rfmaynard/Accel-MagnetoMeter/images/IMG_20181023_001222.jpg

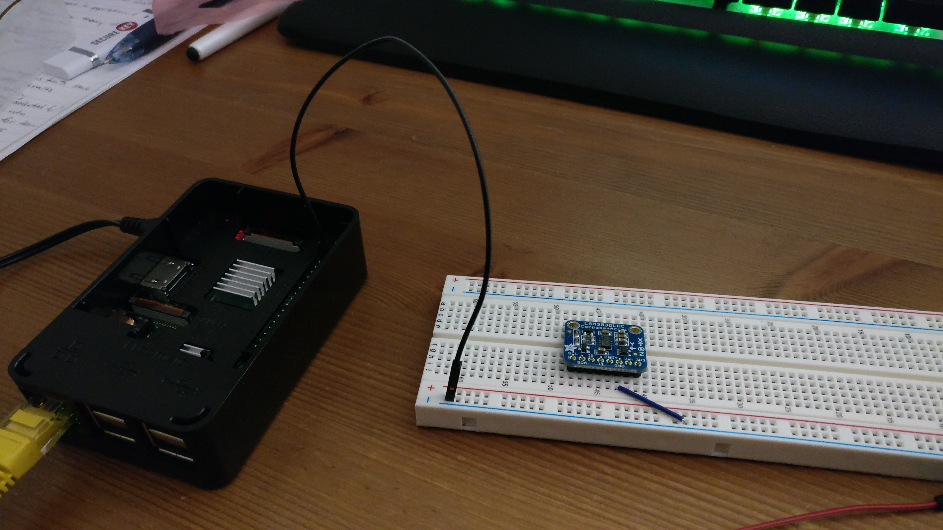
images/IMG_20181023_001222.jpg
