rfmaynard/Accel-MagnetoMeter/images/IMG_20181023_002304.jpg

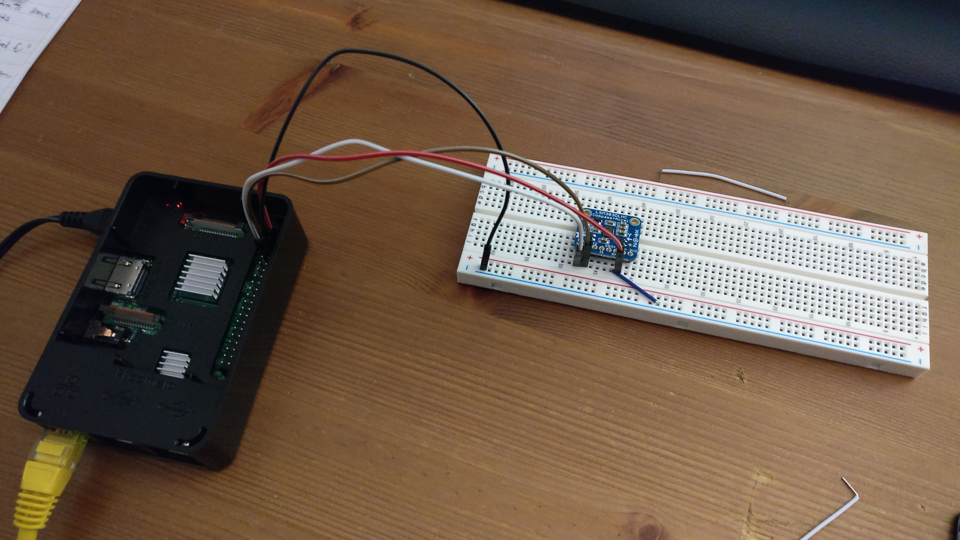
images/IMG_20181023_002304.jpg
