rfmaynard/Accel-MagnetoMeter/images/IMG_20181023_112441.jpg

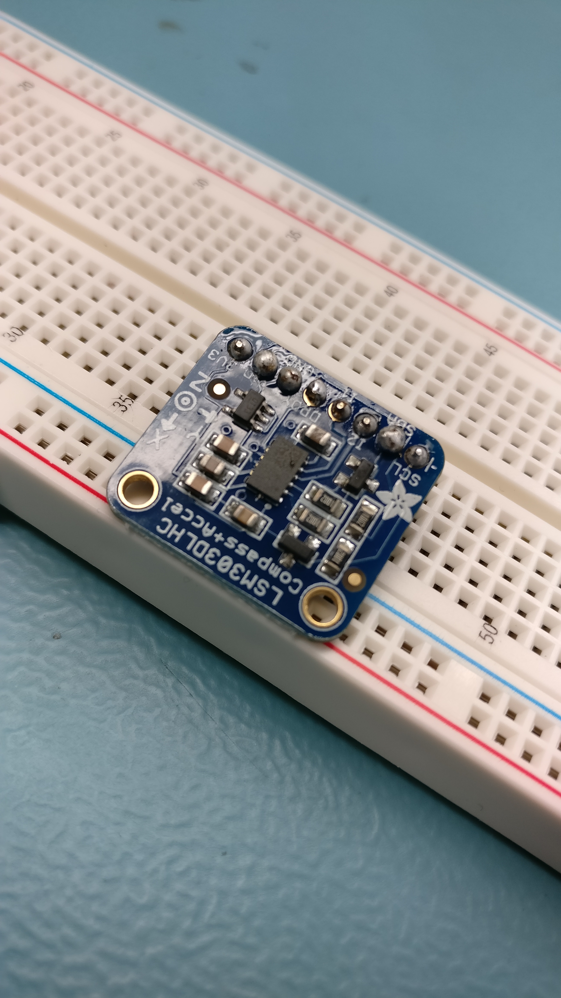
images/IMG_20181023_112441.jpg
