rfmaynard/Accel-MagnetoMeter/images/IMG_20181023_121612.jpg

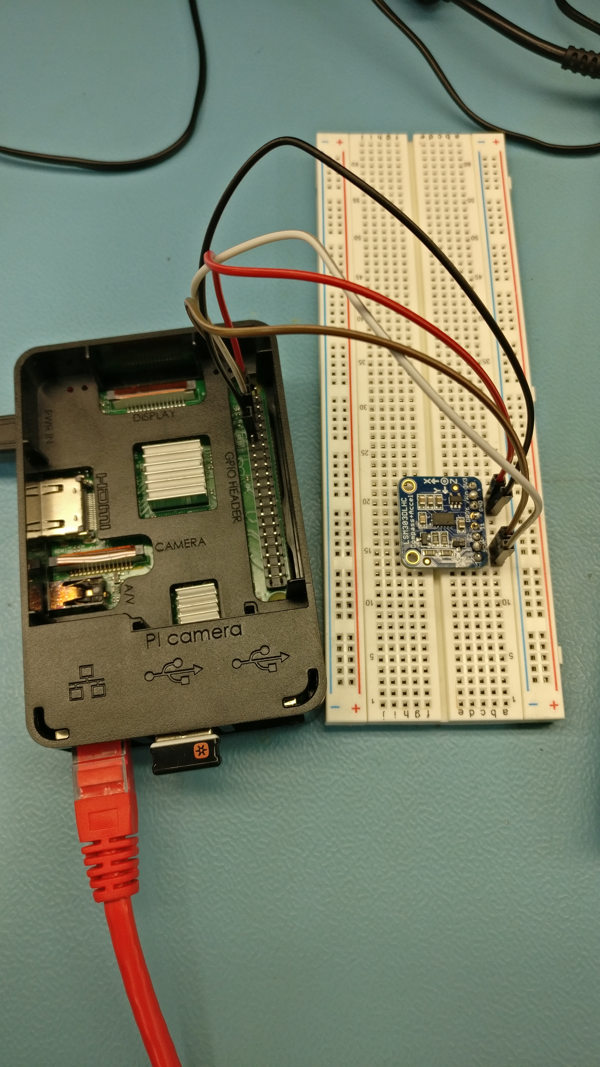
images/IMG_20181023_121612.jpg
