rfmaynard/Accel-MagnetoMeter/images/IMG_20181106_105713.jpg

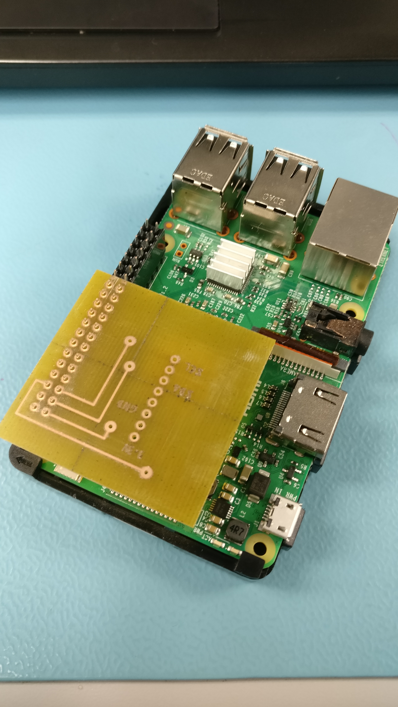
images/IMG_20181106_105713.jpg
