rfmaynard/Accel-MagnetoMeter/images/IMG_20181106_105935.jpg

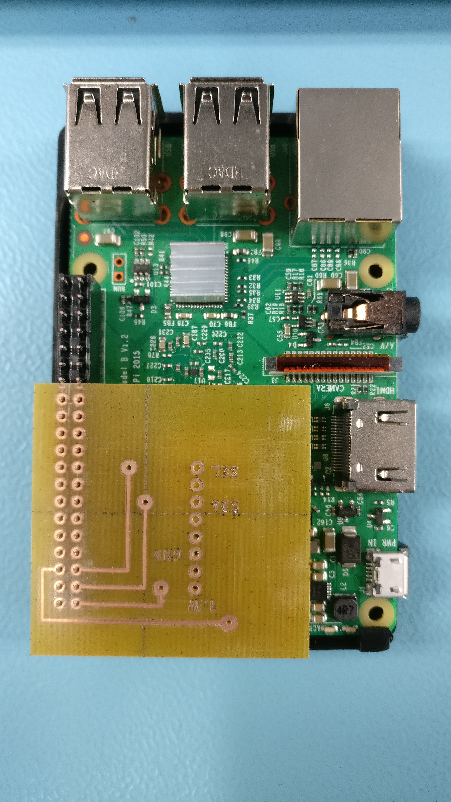
images/IMG_20181106_105935.jpg
