rfmaynard/Accel-MagnetoMeter/images/IMG_20181106_105943.jpg

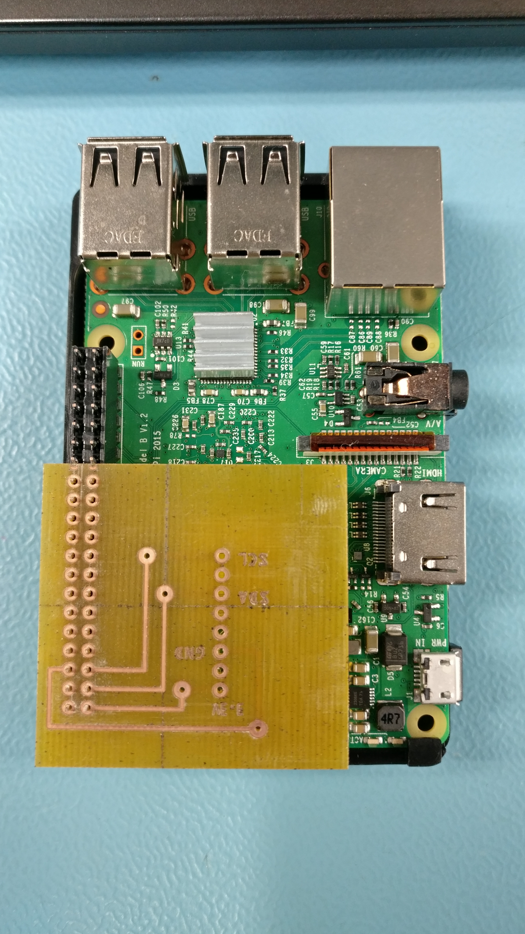
images/IMG_20181106_105943.jpg
