rfmaynard/Accel-MagnetoMeter/images/IMG_20181106_113040.jpg

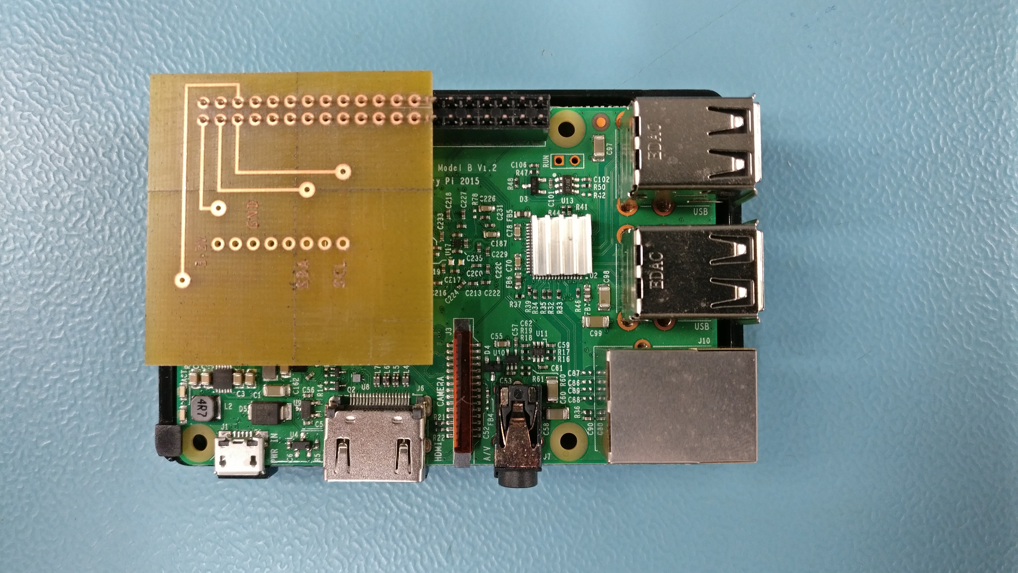
images/IMG_20181106_113040.jpg
