rfmaynard/Accel-MagnetoMeter/images/IMG_20181106_114735.jpg

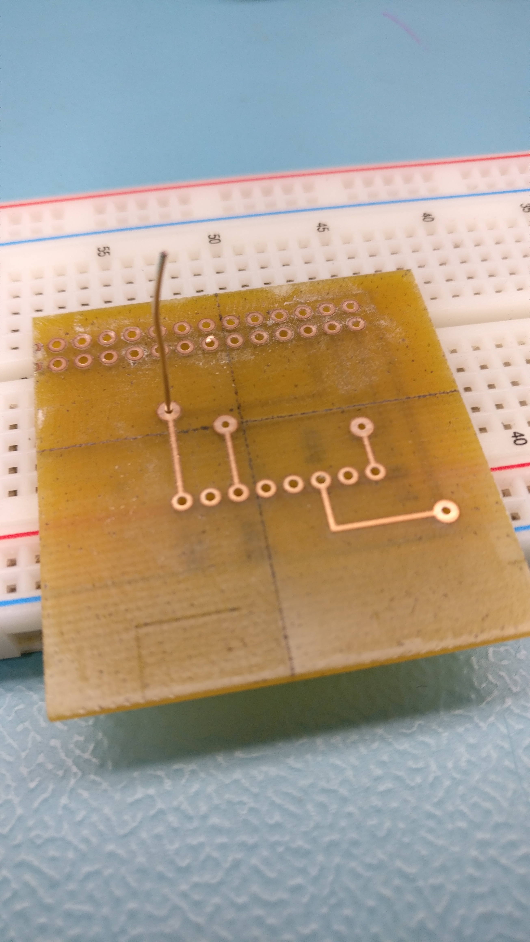
images/IMG_20181106_114735.jpg
