rfmaynard/Accel-MagnetoMeter/images/IMG_20181106_120816.jpg

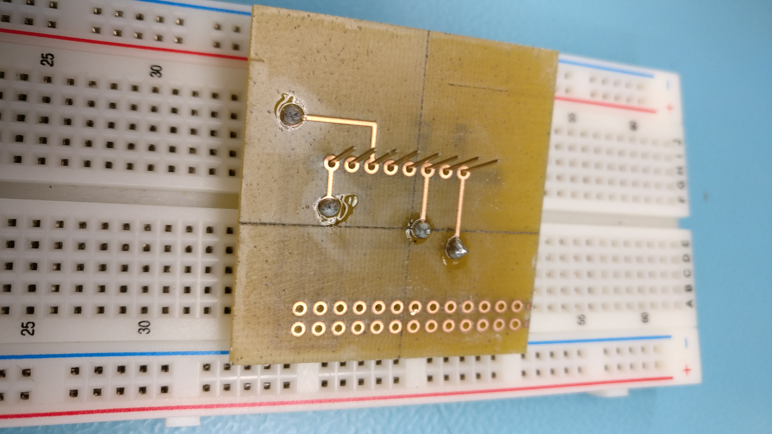
images/IMG_20181106_120816.jpg
