rfmaynard/Accel-MagnetoMeter/images/IMG_20181113_110009.jpg

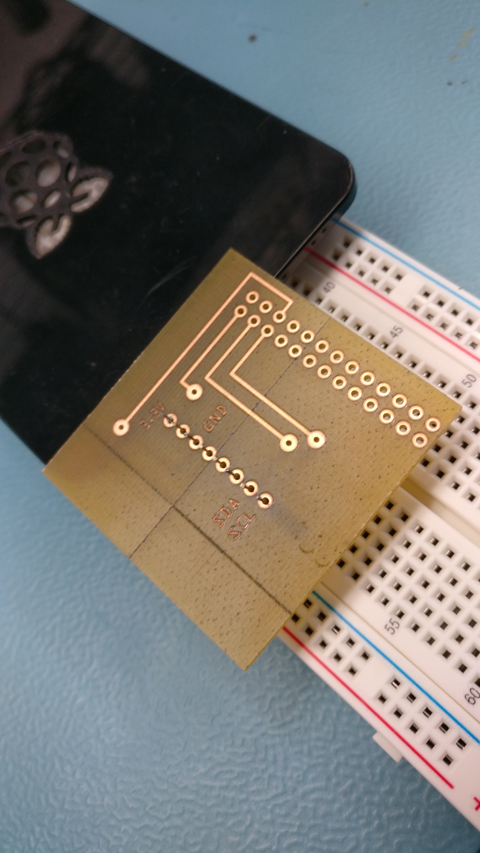
images/IMG_20181113_110009.jpg
