rfmaynard/Accel-MagnetoMeter/images/IMG_20181113_114908.jpg

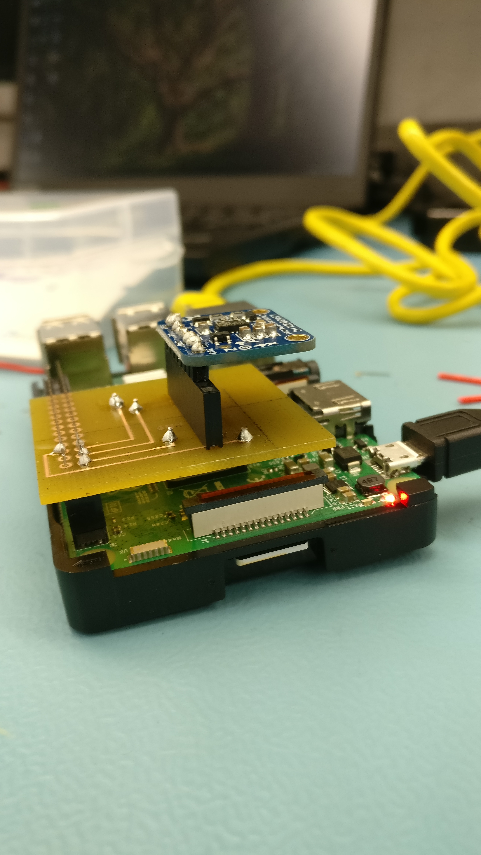
images/IMG_20181113_114908.jpg
