rfmaynard/Accel-MagnetoMeter/images/IMG_20181120_195526.jpg

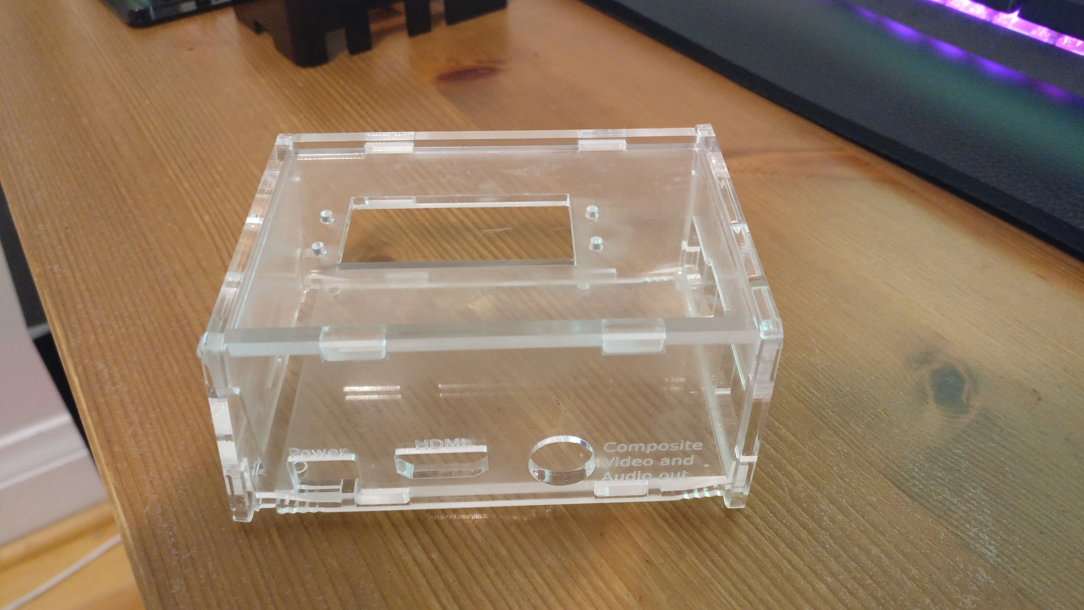
images/IMG_20181120_195526.jpg
