rfmaynard/Accel-MagnetoMeter/images/IMG_20181121_161257.jpg

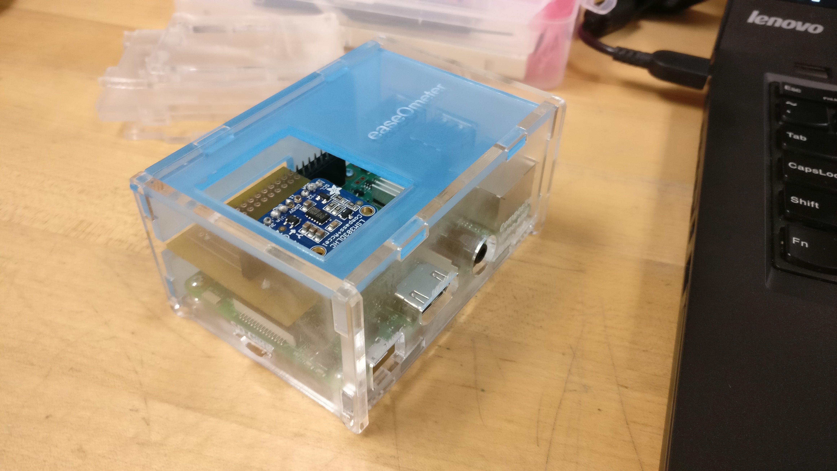
images/IMG_20181121_161257.jpg
