rfmaynard/Accel-MagnetoMeter/images/IMG_20181121_162035.jpg

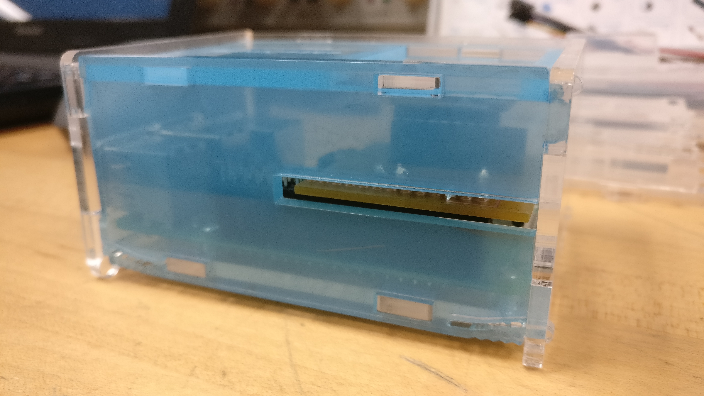
images/IMG_20181121_162035.jpg
