rfmaynard/Accel-MagnetoMeter/images/IMG_20181125_155530.jpg

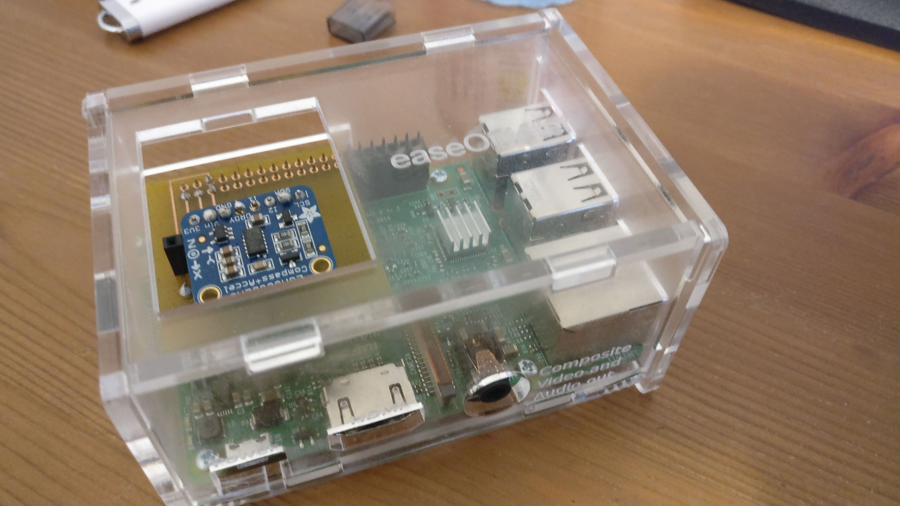
images/IMG_20181125_155530.jpg
