rfmaynard/Accel-MagnetoMeter/images/IMG_20181125_155533.jpg

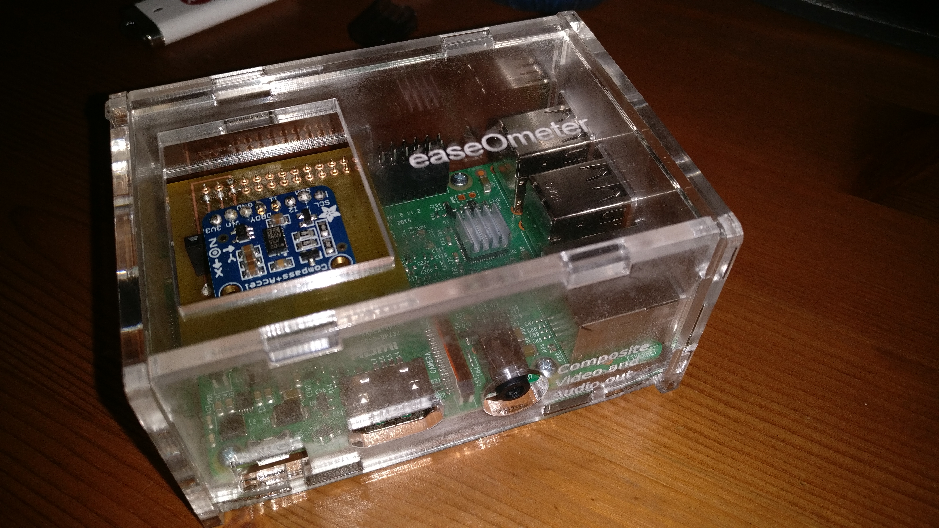
images/IMG_20181125_155533.jpg
